CheimaAmmar/BioSense/Kicad/sscs_kicad.kicad_sch

## KiCad design Kicad/sscs_kicad.kicad_sch (2026-04-25)

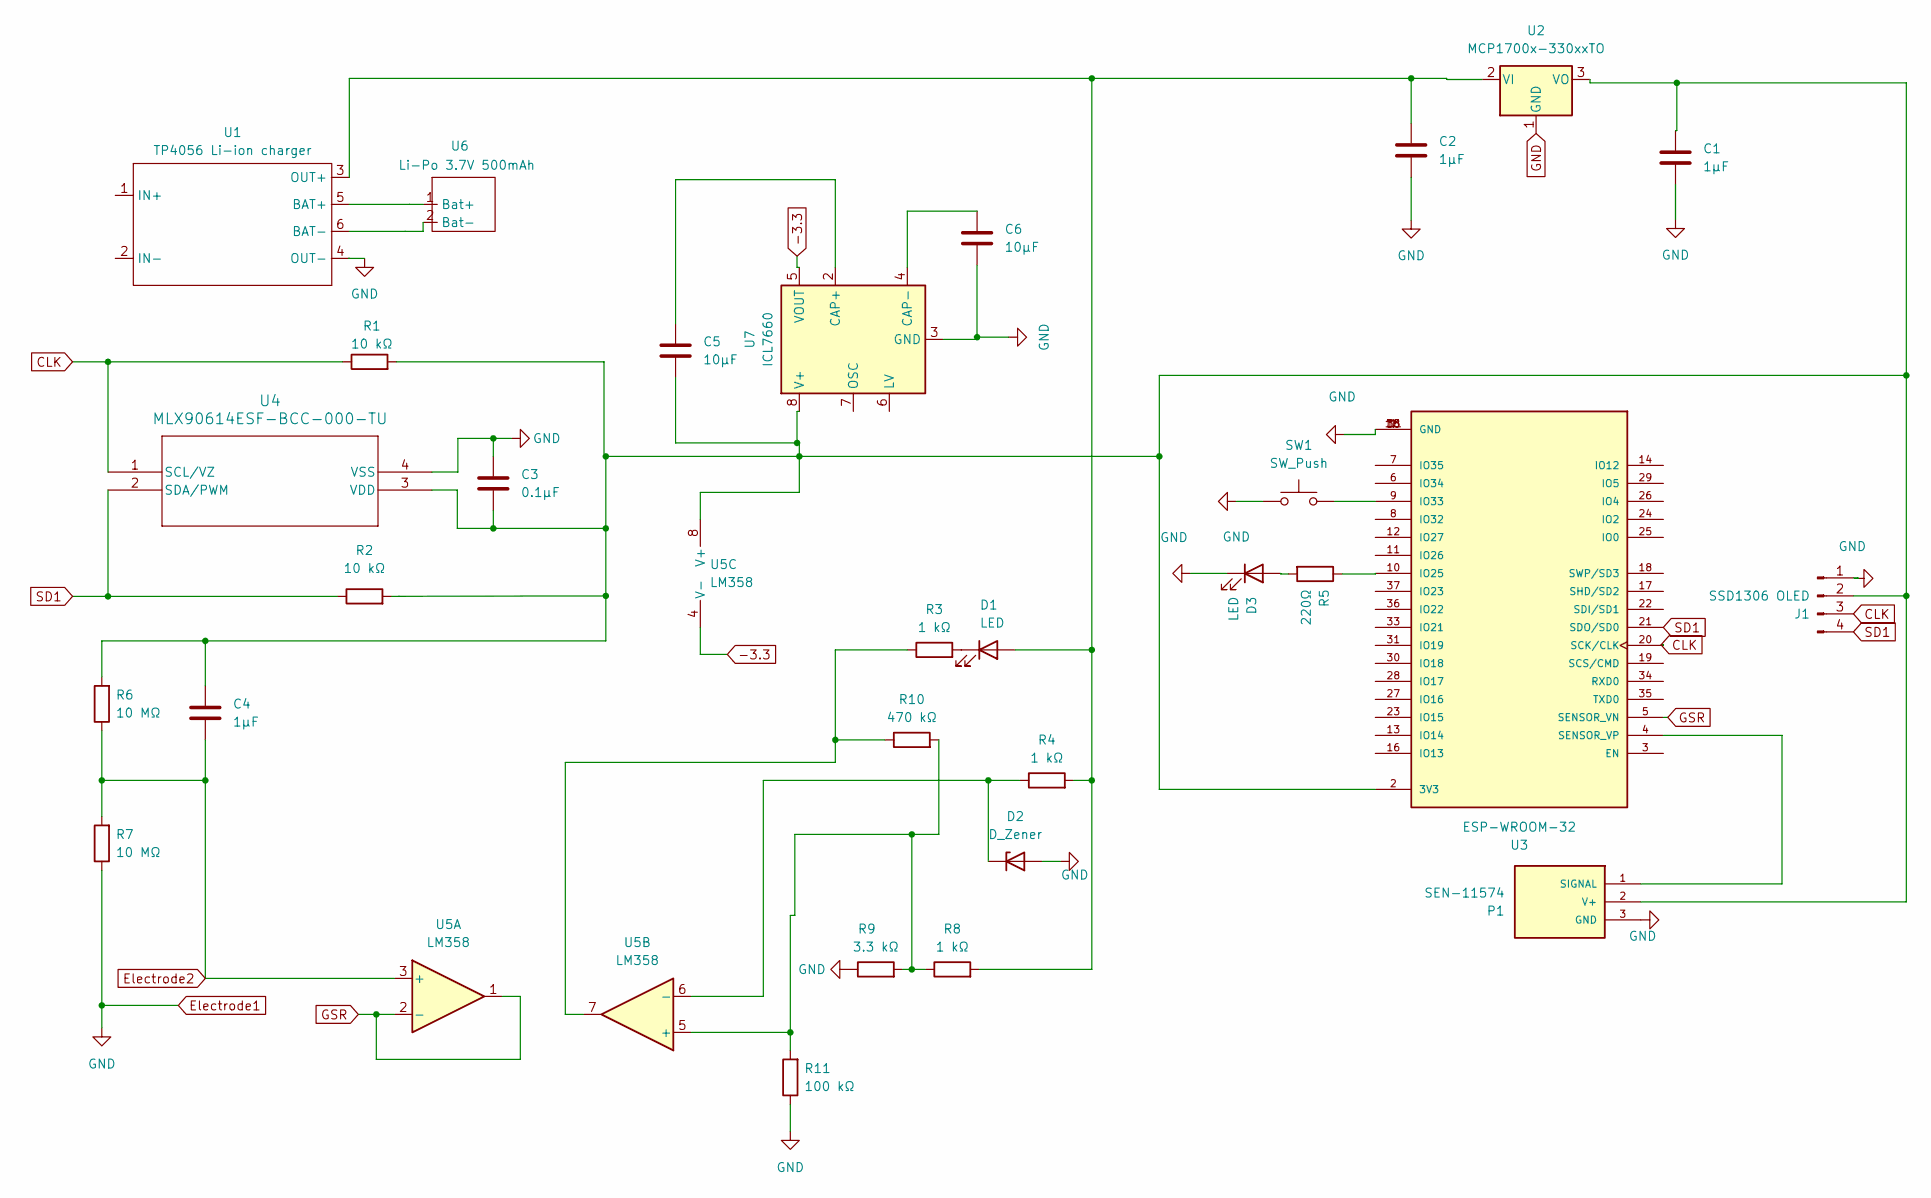
[picture p7: schematic sscs_kicad.kicad_sch]

Parts:
C1, C2, C4: 1µF; C_0805_2012Metric
C3: 0.1µF; C_0603_1608Metric
C5, C6: 10µF; C_0805_2012Metric
D1, D3: LED; LED_D5.0mm
D2: D_Zener; D_T-1_P5.08mm_Horizontal
J1: SSD1306 OLED; FanPinHeader_1x04_P2.54mm_Vertical
P1: SEN-11574; XDCR_SEN-11574
R1, R2: 10 kΩ; R_0805_2012Metric
R3, R4, R8: 1 kΩ; R_0805_2012Metric
R5: 220Ω; R_0805_2012Metric
R6, R7: 10 MΩ; R_0805_2012Metric
R9: 3.3 kΩ; R_0805_2012Metric
R10: 470 kΩ; R_0805_2012Metric
R11: 100 kΩ; R_0805_2012Metric
SW1: SW_Push; SW_PUSH_6mm_H4.3mm
U1: TP4056 Li-ion charger; TP4056-Module
U2: MCP1700x-330xxTO; TO-92_Inline
U3: ESP-WROOM-32; MODULE_ESP-WROOM-32
U4: MLX90614ESF-BCC-000-TU; MLX90614xCC_MEL
U5: LM358; DIP-8_W7.62mm_LongPads
U6: Li-Po 3.7V 500mAh
U7: ICL7660; DIP-8_W7.62mm_LongPads

Connections:
-3.3: U5.4 (V-), U7.5 (VOUT)
CLK: J1.3, R1.1, U3.20 (SCK/CLK), U4.1 (SCL/VZ)
Electrode1: C1.2, C2.2, C3.1, C6.2, D2.2 (A), D3.1 (K), J1.1, P1.3 (GND), R7.1, R9.1, R11.1, SW1.1, U1.4 (OUT-), U3.1 (GND), U3.1.1 (GND), U3.15 (GND), U3.38 (GND), U4.4 (VSS), U7.3 (GND)
Electrode2: C4.2, R6.1, R7.2, U5.3 (+)
GND: U2.1 (GND)
GSR: U3.5 (SENSOR_VN), U5.1, U5.2 (-)
unnamed: C1.1, C3.2, C4.1, C5.2, J1.2, P1.2 (V+), R1.2, R2.2, R6.2, U2.3 (VO), U3.2 (3V3), U4.3 (VDD), U5.8 (V+), U7.8 (V+)
unnamed: C2.1, D1.2 (A), R4.2, R8.2, U1.3 (OUT+), U2.2 (VI)
unnamed: C5.1, U7.2 (CAP+)
unnamed: C6.1, U7.4 (CAP-)
unnamed: D1.1 (K), R3.2
unnamed: D2.1 (K), R4.1, U5.6 (-)
unnamed: D3.2 (A), R5.2
unnamed: P1.1 (SIGNAL), U3.4 (SENSOR_VP)
unnamed: R5.1, U3.10 (IO25)
unnamed: R3.1, R10.1, U5.7
unnamed: R8.1, R9.2, R10.2, R11.2, U5.5 (+)
unnamed: SW1.2, U3.9 (IO33)
unnamed: U1.5 (BAT+), U6.1 (Bat+)
unnamed: U1.6 (BAT-), U6.2 (Bat-)
SD1: J1.4, R2.1, U3.21 (SDO/SD0), U4.2 (SDA/PWM)
